sp5wwp/M17_ANL_v2/PHOTO2.jpg

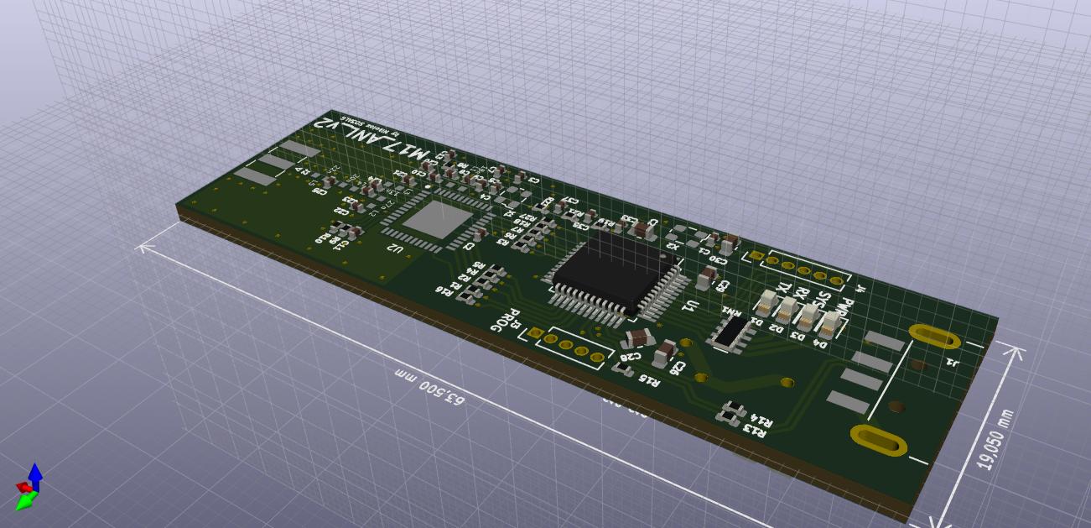
PHOTO2.jpg
