sp5wwp/M17_ANL_v2/PHOTO3.jpg

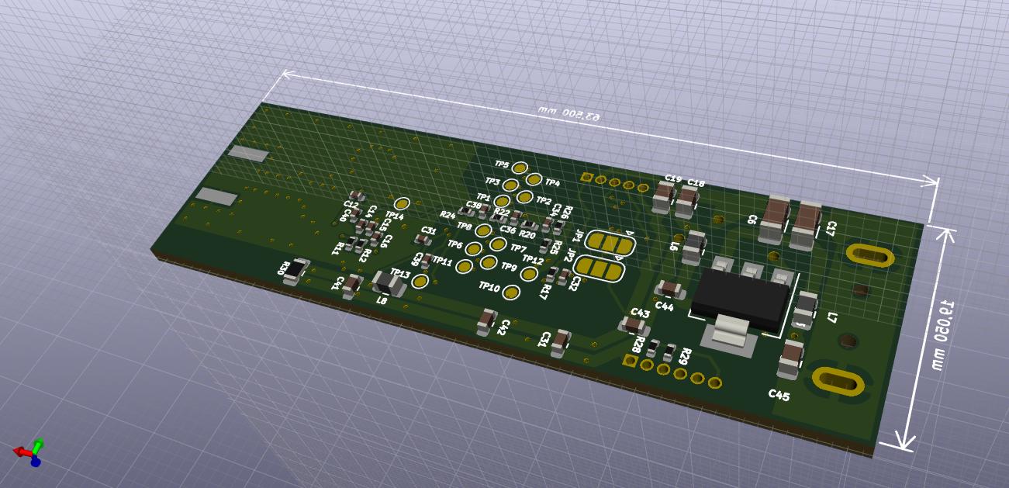
PHOTO3.jpg
